Srivathsan1293/unibots-Third-Timers/media/stepper_motors_drivers.jpg

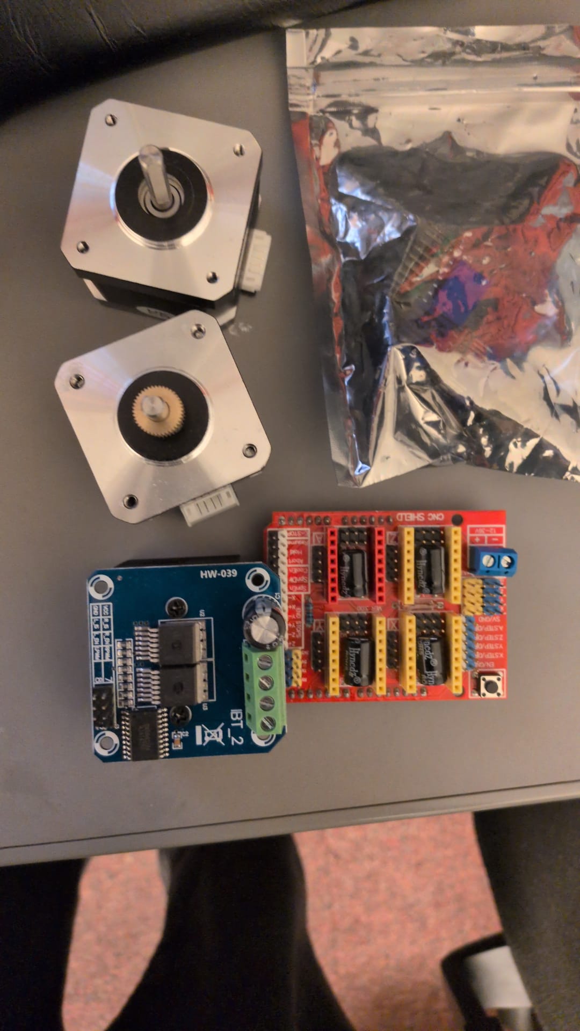
media/stepper_motors_drivers.jpg
