Srivathsan1293/unibots-Third-Timers/media/usb_power_modules.jpg

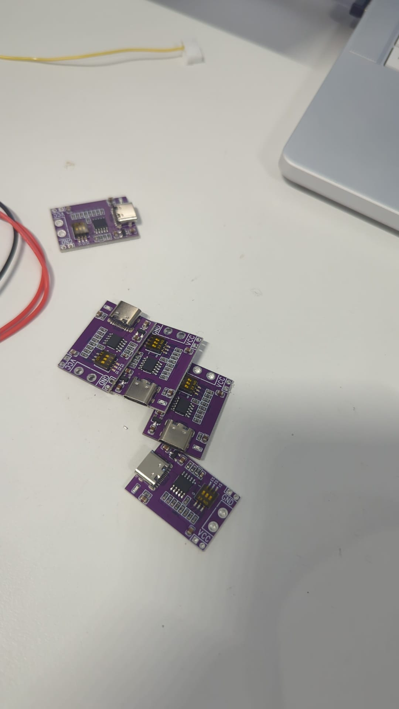
media/usb_power_modules.jpg
