Srivathsan1293/unibots-Third-Timers/app/assets/arena_map.png

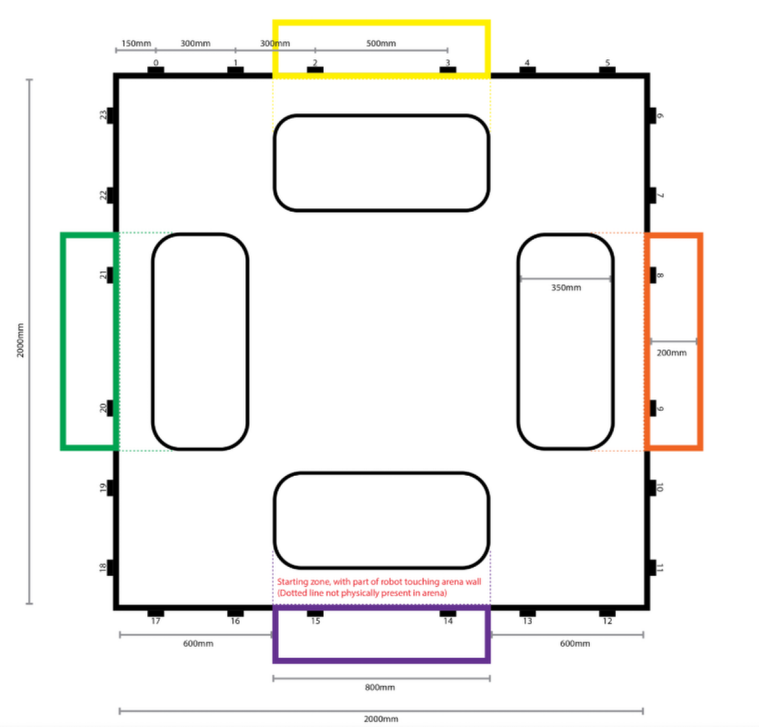
app/assets/arena_map.png
