Srivathsan1293/unibots-Third-Timers/simulation/autonomous_control/webots_env/april_tags/images/tag36_11_00014.png

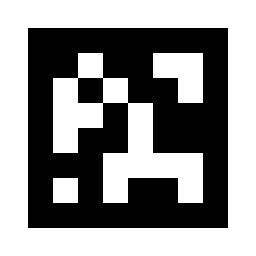
simulation/autonomous_control/webots_env/april_tags/images/tag36_11_00014.png
