Srivathsan1293/unibots-Third-Timers/media/wiring1.jpg

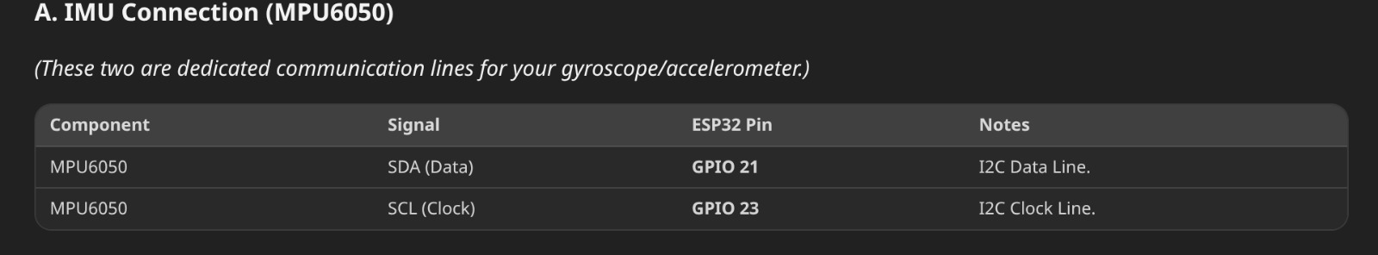
media/wiring1.jpg
