Srivathsan1293/unibots-Third-Timers/media/wiring2.jpg

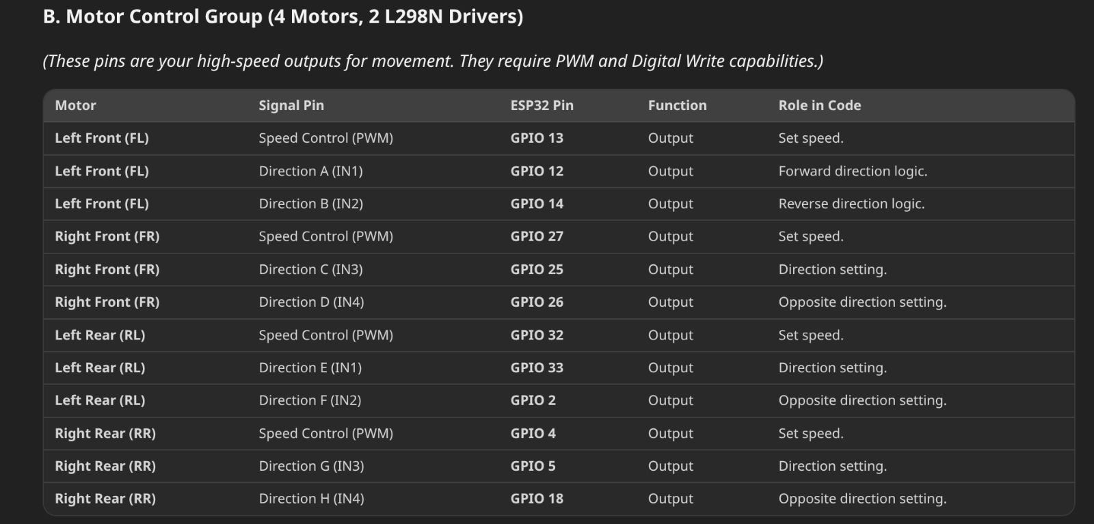
media/wiring2.jpg
