Srivathsan1293/unibots-Third-Timers/media/wiring3.jpg

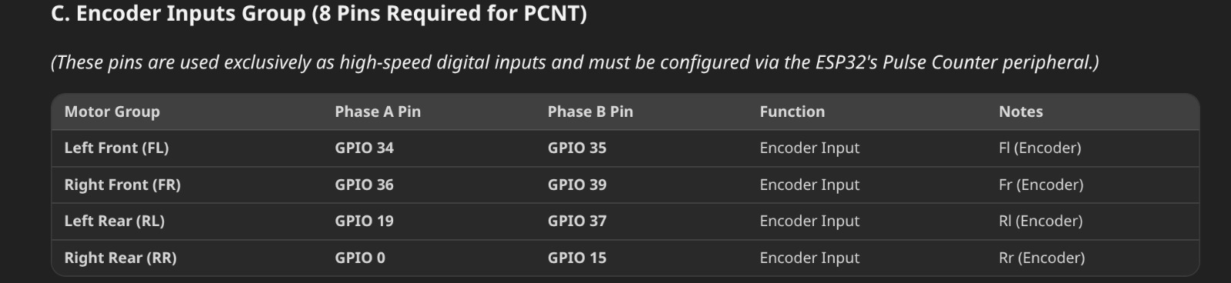
media/wiring3.jpg
